christopher-besch/mold_detect/src/i2c.h

#pragma once

#include "flash_blocks.h"

void i2c_init();

// Ask the sensor about the current atmosphere condition.
// Store those values in sensor_data.
// return 0 on success
// return -1 on failure
int i2c_measure_temp_hum(FlashSensorData* sensor_data);
